tomek-szczesny/OpenUPS/hw/OpenUPS_bat/OpenUPS_bat.kicad_sch

## KiCad design hw/OpenUPS_bat/OpenUPS_bat.kicad_sch (2023-04-22, an earlier design)

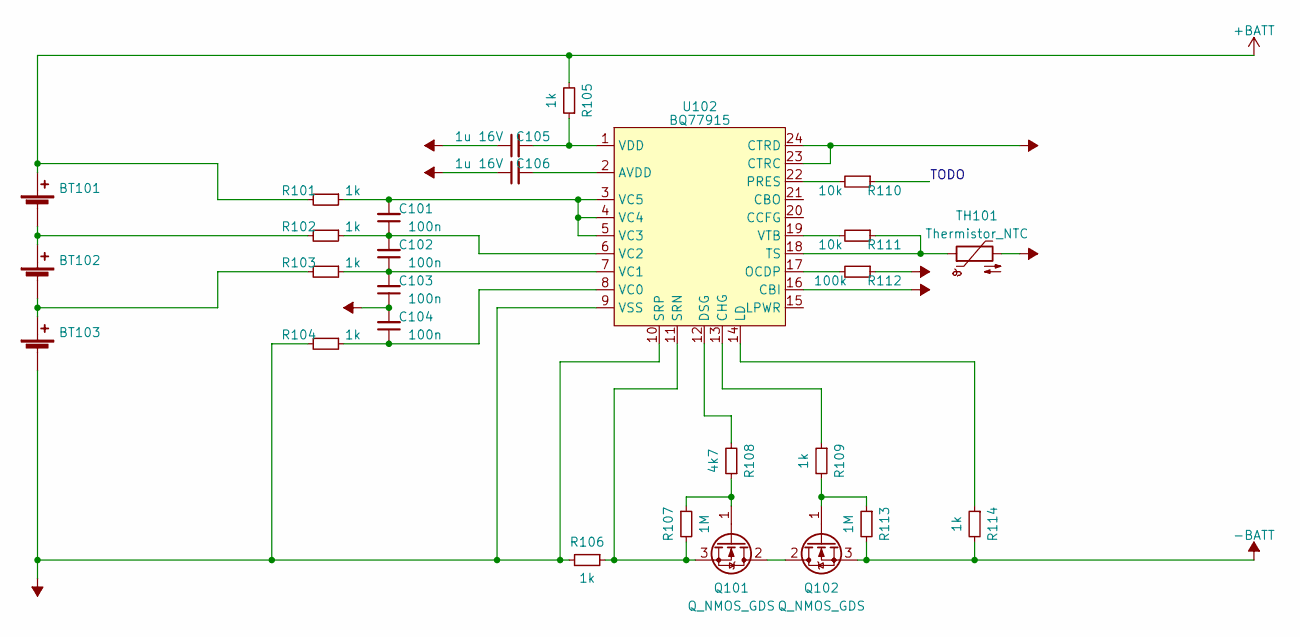
[picture p8: schematic OpenUPS_bat.kicad_sch]

Parts:
BT101, BT102, BT103: Battery_Cell
C101, C102, C103, C104: 100n; C_0603_1608Metric
C105, C106: 1u 16V; C_0603_1608Metric
Q101, Q102: Q_NMOS_GDS; TO-263-2
R101, R102, R103, R104, R105, R106, R109, R114: 1k; R_0603_1608Metric
R107, R113: 1M; R_0603_1608Metric
R108: 4k7; R_0603_1608Metric
R110, R111: 10k; R_0603_1608Metric
R112: 100k; R_0603_1608Metric
TH101: Thermistor_NTC
U102: BQ77915; TSSOP-24_4.4x7.8mm_P0.65mm

Connections:
+BATT: BT101.1 (+), R101.2, R105.2
-BATT: BT103.2 (-), C103.1, C104.2, C105.1, C106.1, Q102.3 (S), R104.2, R106.2, R112.1, R113.2, R114.2, TH101.2, U102.9 (VSS), U102.10 (SRP), U102.16 (CBI), U102.23 (CTRC), U102.24 (CTRD)
unnamed: BT101.2 (-), BT102.1 (+), R102.2
unnamed: BT102.2 (-), BT103.1 (+), R103.2
unnamed: C101.1, C102.2, R102.1, U102.6 (VC2)
unnamed: C101.2, R101.1, U102.3 (VC5), U102.4 (VC4), U102.5 (VC3)
unnamed: C102.1, C103.2, R103.1, U102.7 (VC1)
unnamed: C104.1, R104.1, U102.8 (VC0)
unnamed: C105.2, R105.1, U102.1 (VDD)
unnamed: C106.2, U102.2 (AVDD)
unnamed: Q101.1 (G), R107.1, R108.1
unnamed: Q101.2 (D), Q102.2 (D)
unnamed: Q101.3 (S), R106.1, R107.2, U102.11 (SRN)
unnamed: Q102.1 (G), R109.2, R113.1
unnamed: R108.2, U102.12 (DSG)
unnamed: R109.1, U102.13 (CHG)
unnamed: R110.2, U102.22 (PRES)
unnamed: R111.1, TH101.1, U102.18 (TS)
unnamed: R111.2, U102.19 (VTB)
unnamed: R112.2, U102.17 (OCDP)
unnamed: R114.1, U102.14 (LD)

Notes on the sheet:
TODO
