tomek-szczesny/OpenUPS/hw/OpenUPS_ups/5V_Buck.kicad_sch

## KiCad design hw/OpenUPS_ups/5V_Buck.kicad_sch (2023-05-13, an earlier design)

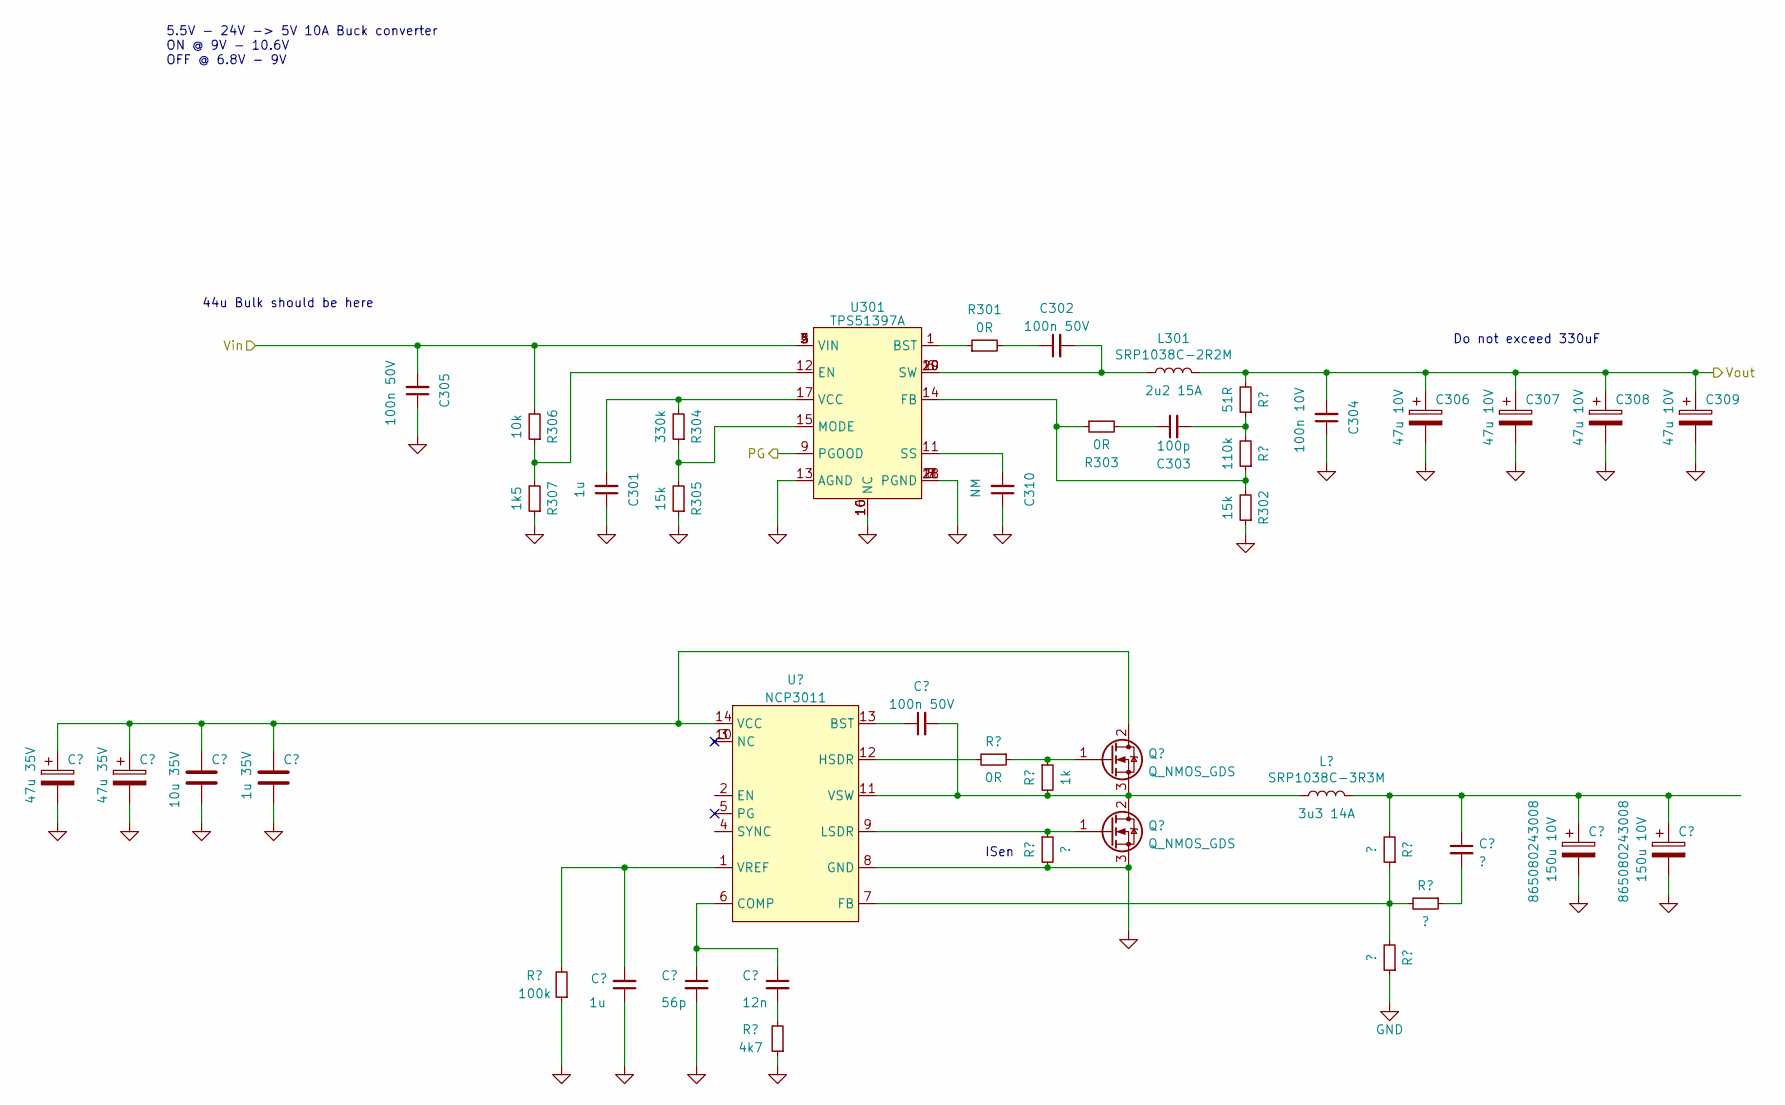
[picture p9: schematic 5V_Buck.kicad_sch]

Parts:
C301: 1u; C_0603_1608Metric
C302, C305: 100n 50V; C_0603_1608Metric
C303: 100p; C_0603_1608Metric
C304: 100n 10V; C_0603_1608Metric
C306, C307, C308, C309: CP_Elec_6.3x5.7
C310: NM; C_0603_1608Metric
L301: SRP1038C-2R2M; L_Bourns_SRP1038C_10.0x10.0mm
R301, R303: 0R; R_0603_1608Metric
R302, R305: 15k; R_0603_1608Metric
R304: 330k; R_0603_1608Metric
R306: 10k; R_0603_1608Metric
R307: 1k5; R_0603_1608Metric
U301: TPS51397A; Texas-VQFN-HR-20_EP_3x3_Pitch0.45mm

Connections:
GND: C301.1, C304.1, C305.1, C306.2, C307.2, C308.2, C309.2, C310.1, R302.1, R305.1, R307.1, U301.7 (PGND), U301.8 (PGND), U301.10 (NC), U301.13 (AGND), U301.16 (NC), U301.18 (PGND), U301.21 (PGND)
unnamed: C301.2, R304.2, U301.17 (VCC)
unnamed: C302.1, R301.2
unnamed: C302.2, L301.1, U301.6 (SW), U301.19 (SW), U301.20 (SW)
unnamed: C303.1, R303.2
unnamed: C310.2, U301.11 (SS)
unnamed: R301.1, U301.1 (BST)
unnamed: R302.2, R303.1, U301.14 (FB)
unnamed: R304.1, R305.2, U301.15 (MODE)
unnamed: R306.1, R307.2, U301.12 (EN)
PG: U301.9 (PGOOD)
Vin: C305.2, R306.2, U301.2 (VIN), U301.3 (VIN), U301.4 (VIN), U301.5 (VIN)
Vout: C304.2, C306.1, C307.1, C308.1, C309.1, L301.2

Notes on the sheet:
5.5V - 24V -> 5V 10A Buck converter ON @ 9V - 10.6V OFF @ 6.8V - 9V
Do not exceed 330uF
ISen
44u Bulk should be here
