tomek-szczesny/OpenUPS/hw/OpenUPS_ups/12V_Buck.kicad_sch

## KiCad design hw/OpenUPS_ups/12V_Buck.kicad_sch (2023-04-21, an earlier design)

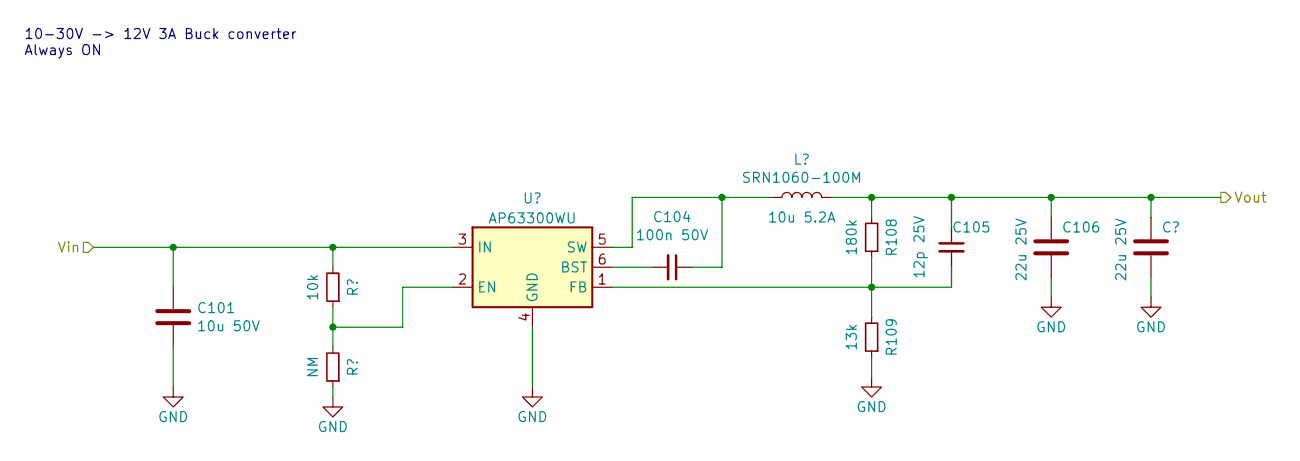
[picture p10: schematic 12V_Buck.kicad_sch]

Parts:
C101: 10u 50V; C_1206_3216Metric
C104: 100n 50V; C_0603_1608Metric
C105: 12p 25V; C_0603_1608Metric
C106: 22u 25V; C_1206_3216Metric
R108: 180k; R_0603_1608Metric
R109: 13k; R_0603_1608Metric

Connections:
GND: C101.2, C106.2, R109.1
unnamed: C105.2, R108.1, R109.2
Vin: C101.1
Vout: C105.1, C106.1, R108.2

Notes on the sheet:
10-30V -> 12V 3A Buck converter Always ON
