tomek-szczesny/OpenUPS/hw/OpenUPS_ups/12V_Buck_Boost.kicad_sch

## KiCad design hw/OpenUPS_ups/12V_Buck_Boost.kicad_sch (2023-05-13, an earlier design)

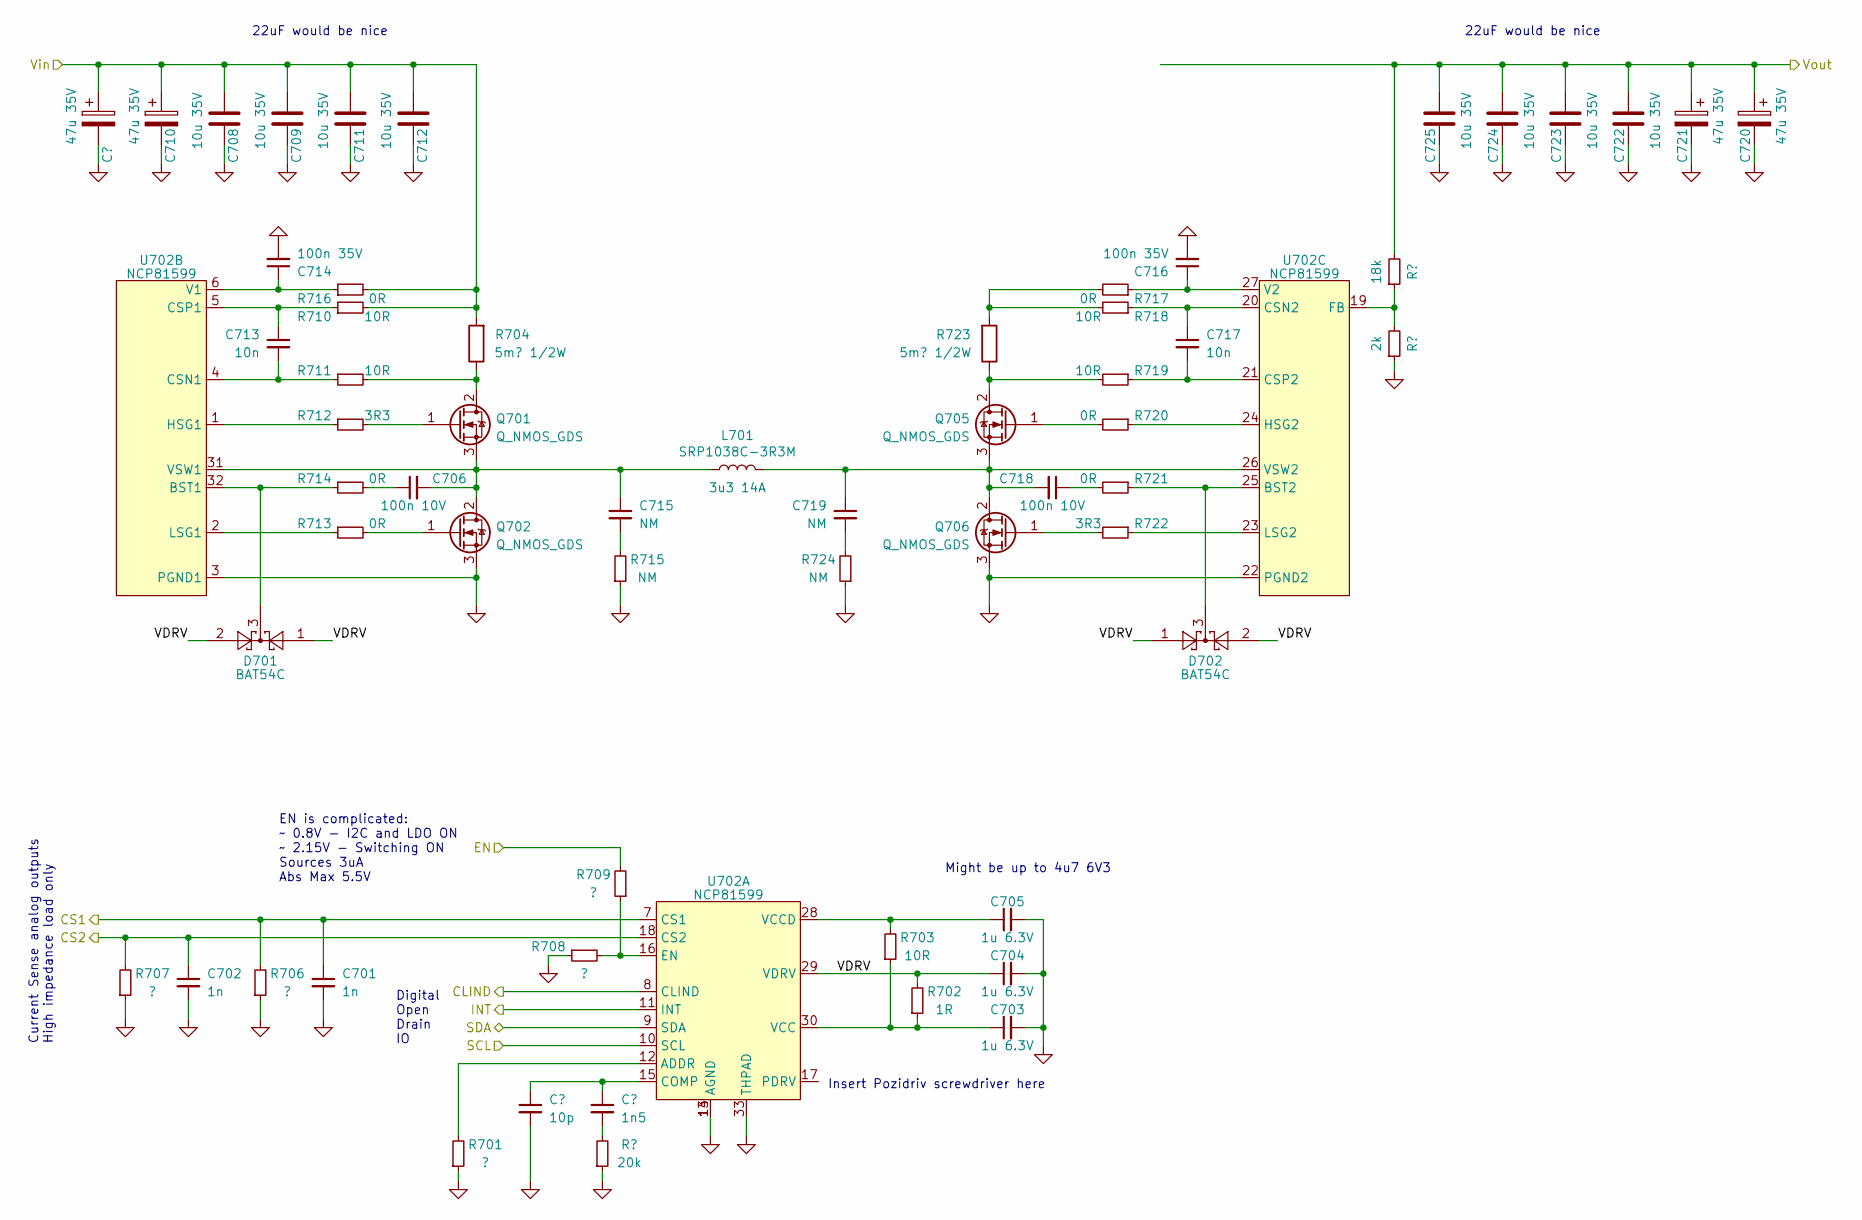
[picture p11: schematic 12V_Buck_Boost.kicad_sch]

Parts:
C701, C702: 1n; C_0603_1608Metric
C703, C704, C705: 1u 6.3V; C_0603_1608Metric
C706, C718: 100n 10V; C_0603_1608Metric
C708, C709, C711, C712, C722, C723, C724, C725: 10u 35V; C_1206_3216Metric
C710, C720, C721: 47u 35V; CP_Elec_6.3x7.7
C713, C717: 10n; C_0603_1608Metric
C714, C716: 100n 35V; C_0603_1608Metric
C715, C719: NM; C_0603_1608Metric
D701, D702: BAT54C; SOT-23
L701: SRP1038C-3R3M; L_Bourns_SRP1038C_10.0x10.0mm
Q701, Q702, Q705, Q706: Q_NMOS_GDS; TO-263-2
R701, R706, R707, R708, R709: ?; R_0603_1608Metric
R702: 1R; R_0603_1608Metric
R703, R710, R711, R718, R719: 10R; R_0603_1608Metric
R704, R723: 5m? 1/2W; R_2512_6332Metric
R712, R722: 3R3; R_0603_1608Metric
R713, R714, R716, R717, R720, R721: 0R; R_0603_1608Metric
R715, R724: NM; R_0603_1608Metric
U702: NCP81599; QFN-32-1EP_5x5mm_P0.5mm_EP3.7x3.7mm

Connections:
CLIND: U702.8 (CLIND)
CS1: C701.1, R706.2, U702.7 (CS1)
CS2: C702.1, R707.2, U702.18 (CS2)
EN: R709.2
GND: C701.2, C702.2, C703.2, C704.2, C705.2, C710.2, C711.2, C712.2, C714.2, C716.2, C720.2, C721.2, C722.2, C723.2, C724.2, C725.2, Q702.3 (S), Q706.3 (S), R701.1, R706.1, R707.1, R708.1, R715.1, R724.1, U702.3 (PGND1), U702.13 (AGND), U702.14 (AGND), U702.22 (PGND2), U702.33 (THPAD)
INT: U702.11 (INT)
unnamed: C703.1, R702.1, R703.1, U702.30 (VCC)
unnamed: C705.1, R703.2, U702.28 (VCCD)
unnamed: C706.1, R714.2
unnamed: C706.2, C715.1, L701.1, Q701.3 (S), Q702.2 (D), U702.31 (VSW1)
unnamed: C713.1, R710.1, U702.5 (CSP1)
unnamed: C713.2, R711.1, U702.4 (CSN1)
unnamed: C714.1, R716.1, U702.6 (V1)
unnamed: C715.2, R715.2
unnamed: C716.1, R717.1, U702.27 (V2)
unnamed: C717.1, R718.1, U702.20 (CSN2)
unnamed: C717.2, R719.1, U702.21 (CSP2)
unnamed: C718.1, R721.2
unnamed: C718.2, C719.1, L701.2, Q705.3 (S), Q706.2 (D), U702.26 (VSW2)
unnamed: C719.2, R724.2
unnamed: D701.3, R714.1, U702.32 (BST1)
unnamed: D702.3, R721.1, U702.25 (BST2)
unnamed: Q701.1 (G), R712.2
unnamed: Q701.2 (D), R704.1, R711.2
unnamed: Q702.1 (G), R713.2
unnamed: Q705.1 (G), R720.2
unnamed: Q705.2 (D), R719.2, R723.1
unnamed: Q706.1 (G), R722.2
unnamed: R701.2, U702.12 (ADDR)
unnamed: R708.2, R709.1, U702.16 (EN)
unnamed: R712.1, U702.1 (HSG1)
unnamed: R713.1, U702.2 (LSG1)
unnamed: R717.2, R718.2, R723.2
unnamed: R720.1, U702.24 (HSG2)
unnamed: R722.1, U702.23 (LSG2)
SCL: U702.10 (SCL)
SDA: U702.9 (SDA)
VDRV: C704.1, D701.1, D701.2, D702.1, D702.2, R702.2, U702.29 (VDRV)
Vin: C708.1, C709.1, C710.1, C711.1, C712.1, R704.2, R710.2, R716.2
Vout: C720.1, C721.1, C722.1, C723.1, C724.1, C725.1

Notes on the sheet:
Insert Pozidriv screwdriver here
Digital Open Drain IO
Might be up to 4u7 6V3
Current Sense analog outputs High impedance load only
22uF would be nice
EN is complicated: ~ 0.8V - I2C and LDO ON ~ 2.15V - Switching ON Sources 3uA Abs Max 5.5V
