tomek-szczesny/OpenUPS/hw/OpenUPS_ups/Bat_Charger.kicad_sch

## KiCad design hw/OpenUPS_ups/Bat_Charger.kicad_sch (2023-05-13, an earlier design)

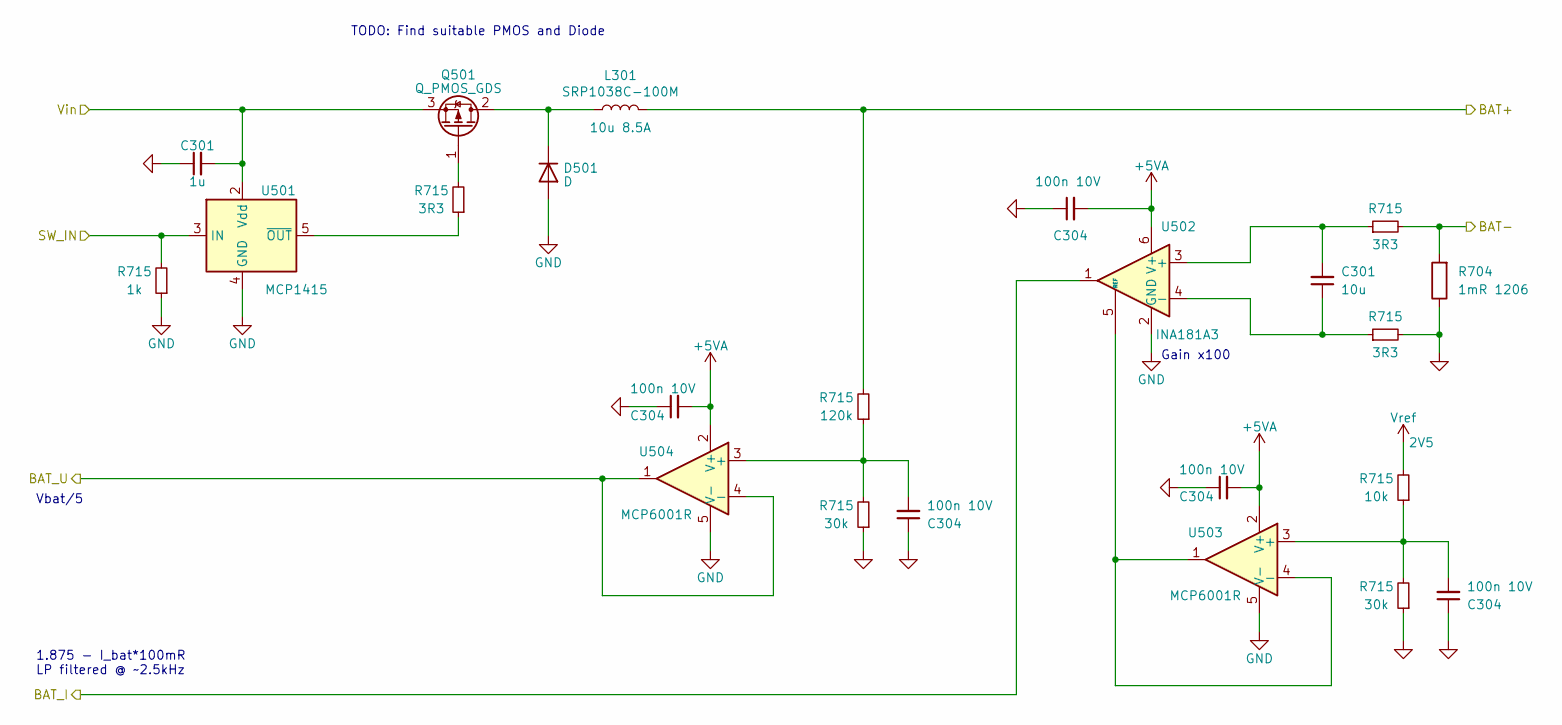
[picture p12: schematic Bat_Charger.kicad_sch]

Parts:
C301: 1u; C_0603_1608Metric
C304: 100n 10V; C_0603_1608Metric
D501: D
L301: SRP1038C-100M; L_Bourns_SRP1038C_10.0x10.0mm
Q501: Q_PMOS_GDS
R704: 1mR 1206; R_1206_3216Metric
R715: 3R3; R_0603_1608Metric
U501: MCP1415; SOT-23-5
U502: INA181A3; SOT-23-6
U503, U504: MCP6001R; SOT-23-5

Connections:
+5VA: C304.2, U502.6 (V+), U503.2 (V+), U504.2 (V+)
BAT+: L301.2, R715.2
BAT-: R704.2, R715.2
BAT_I: U502.1
BAT_U: U504.1, U504.4 (-)
GND: C301.1, C304.1, D501.2 (A), R704.1, R715.1, R715.2, U501.4 (GND), U502.2 (GND), U503.5 (V-), U504.5 (V-)
unnamed: C301.1, R715.1, U502.4 (-)
unnamed: C301.2, R715.1, U502.3 (+)
unnamed: C304.2, R715.1, R715.2, U503.3 (+), U504.3 (+)
unnamed: D501.1 (K), L301.1, Q501.2 (D)
unnamed: Q501.1 (G), R715.2
unnamed: R715.1, U501.5 (~OUT)
unnamed: U502.5 (REF), U503.1, U503.4 (-)
SW_IN: R715.2, U501.3 (IN)
Vin: C301.2, Q501.3 (S), U501.2 (Vdd)
Vref: R715.2

Notes on the sheet:
1.875 - I_bat*100mR LP filtered @ ~2.5kHz
Vbat/5
TODO: Find suitable PMOS and Diode
Gain x100
