tomek-szczesny/OpenUPS/hw/OpenUPS_ups/aux.kicad_sch

## KiCad design hw/OpenUPS_ups/aux.kicad_sch (2023-05-13)

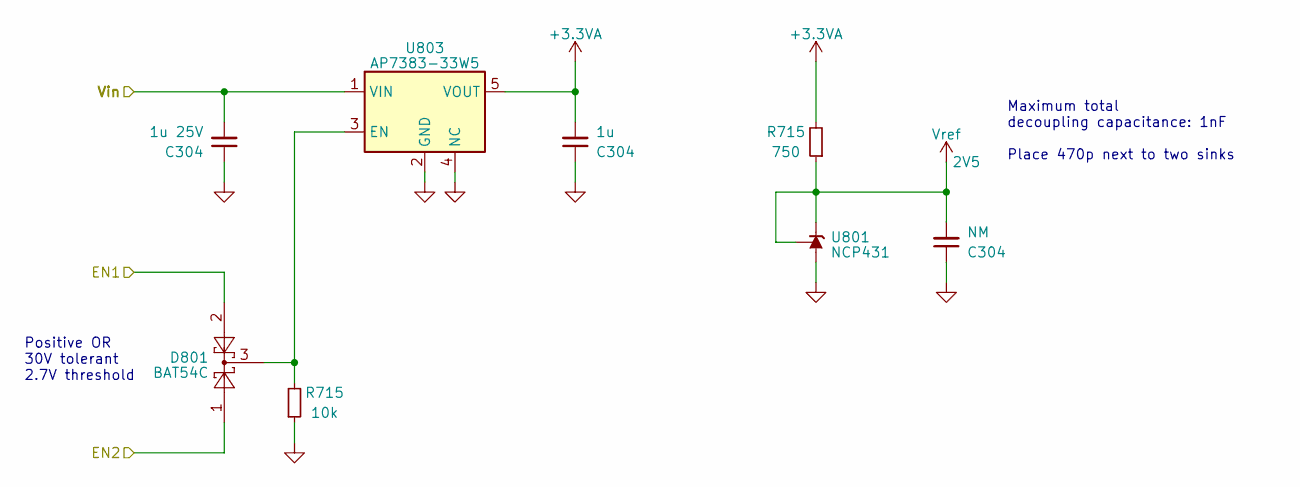
[picture p13: schematic aux.kicad_sch]

Parts:
C304: 1u; C_0603_1608Metric
D801: BAT54C; SOT-23
R715: 10k; R_0603_1608Metric
U801: NCP431; SOT-23
U803: AP7383-33W5; SOT-23-5

Connections:
+3.3VA: C304.2, R715.2, U803.5 (VOUT)
EN1: D801.2
EN2: D801.1
GND: C304.1, R715.1, U801.3 (A), U803.2 (GND), U803.4 (NC)
unnamed: D801.3, R715.2, U803.3 (EN)
Vin: C304.2, U803.1 (VIN)
Vref: C304.2, R715.1, U801.1 (REF), U801.2 (K)

Notes on the sheet:
Maximum total decoupling capacitance: 1nF Place 470p next to two sinks
Positive OR 30V tolerant 2.7V threshold
