tomek-szczesny/OpenUPS/hw/OpenUPS_ups/ext_i2c.kicad_sch

## KiCad design hw/OpenUPS_ups/ext_i2c.kicad_sch (2023-05-13)

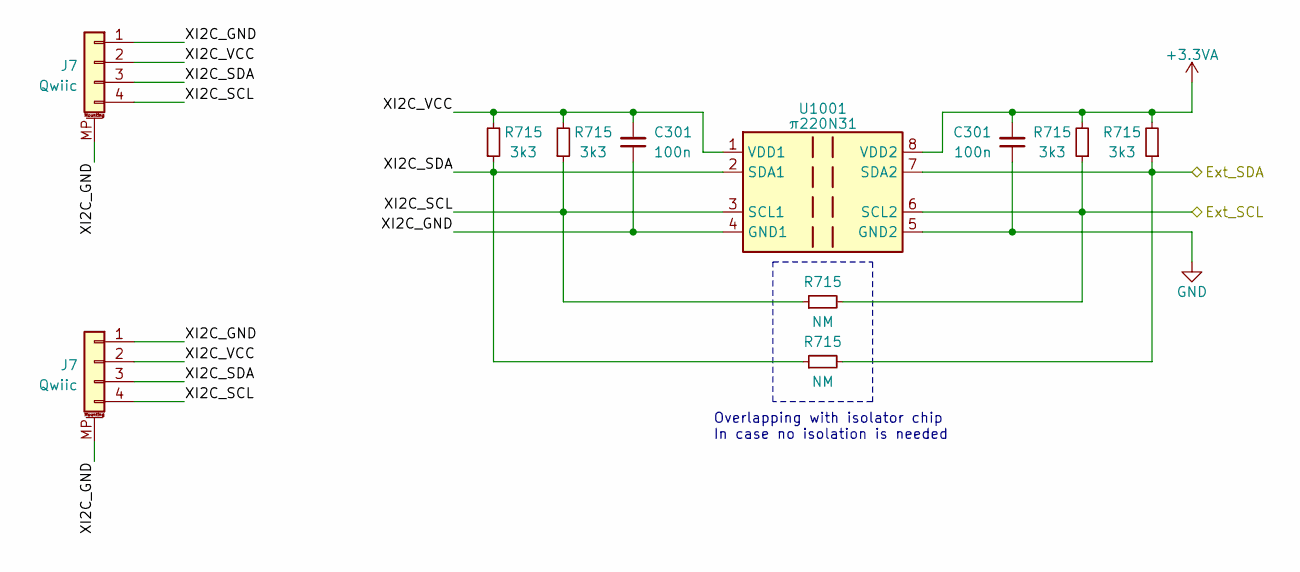
[picture p14: schematic ext_i2c.kicad_sch]

Parts:
C301: 100n; C_0603_1608Metric
J7: Qwiic; JST_SH_SM04B-SRSS-TB_1x04-1MP_P1.00mm_Horizontal
R715: NM
U1001: π220N31; SO-8_3.9x4.9mm_P1.27mm

Connections:
+3.3VA: C301.2, R715.2, U1001.8 (VDD2)
Ext_SCL: R715.1, R715.2, U1001.6 (SCL2)
Ext_SDA: R715.1, R715.2, U1001.7 (SDA2)
GND: C301.1, U1001.5 (GND2)
XI2C_GND: C301.1, J7.1, J7.MP (MountPin), U1001.4 (GND1)
XI2C_SCL: J7.4, R715.1, U1001.3 (SCL1)
XI2C_SDA: J7.3, R715.1, U1001.2 (SDA1)
XI2C_VCC: C301.2, J7.2, R715.2, U1001.1 (VDD1)

Notes on the sheet:
Overlapping with isolator chip In case no isolation is needed
