tomek-szczesny/OpenUPS/hw/OpenUPS_ups/fans.kicad_sch

## KiCad design hw/OpenUPS_ups/fans.kicad_sch (2023-05-13)

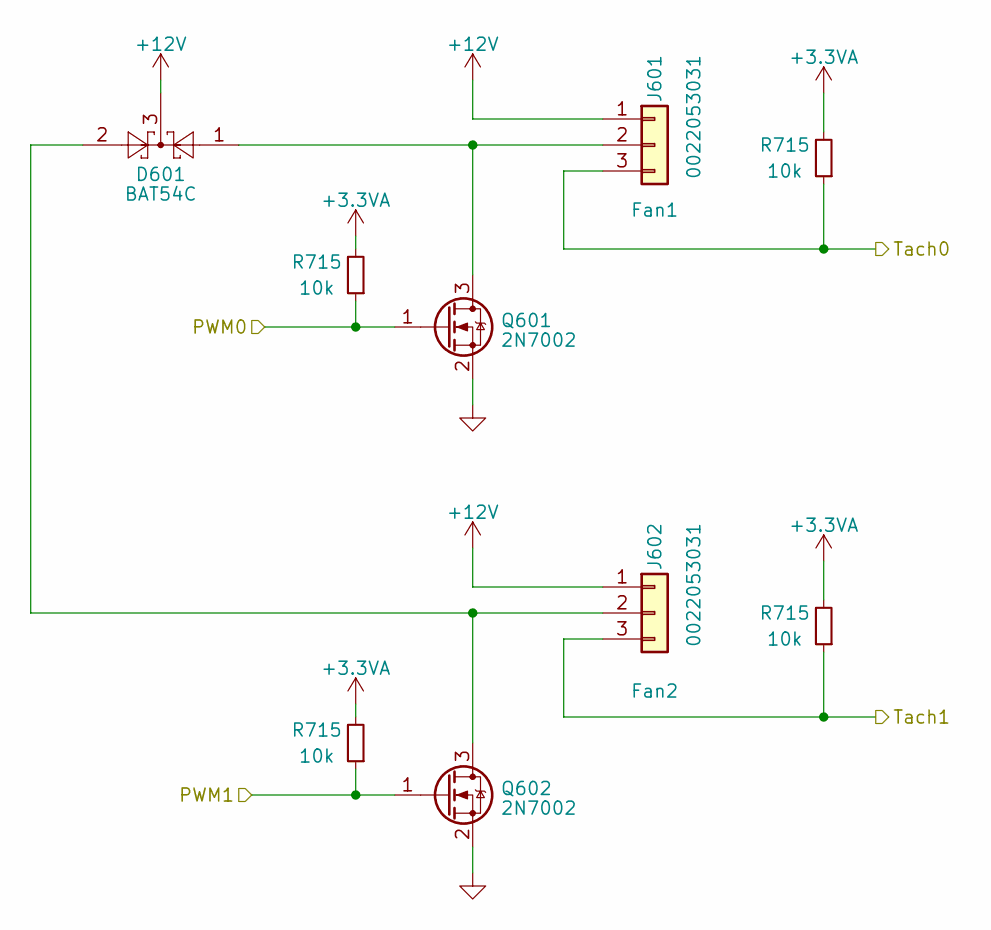
[picture p15: schematic fans.kicad_sch]

Parts:
D601: BAT54C; SOT-23
J601, J602: 0022053031; Molex-22-05-3031-MFG
Q601, Q602: 2N7002; SOT-23
R715: 10k; R_0603_1608Metric

Connections:
+3.3VA: R715.2
+12V: D601.3, J601.1, J602.1
GND: Q601.2 (S), Q602.2 (S)
unnamed: D601.1, J601.2, Q601.3 (D)
unnamed: D601.2, J602.2, Q602.3 (D)
PWM0: Q601.1 (G), R715.1
PWM1: Q602.1 (G), R715.1
Tach0: J601.3, R715.1
Tach1: J602.3, R715.1
