tomek-szczesny/OpenUPS/hw/OpenUPS_ups/leds.kicad_sch

## KiCad design hw/OpenUPS_ups/leds.kicad_sch (2023-05-13)

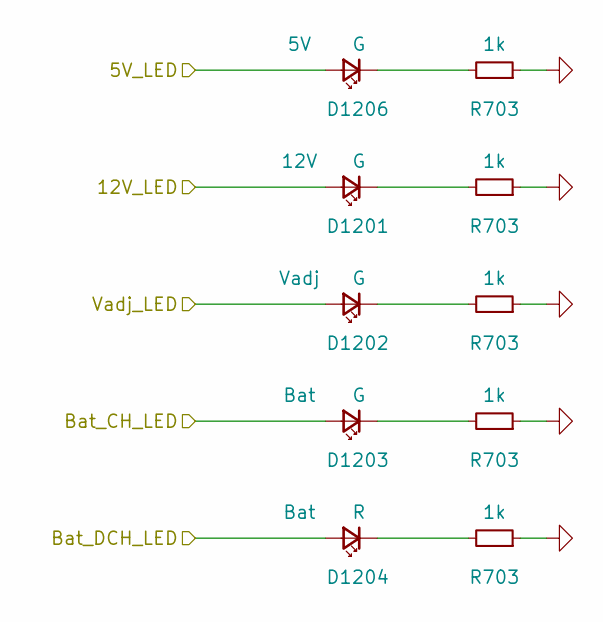
[picture p16: schematic leds.kicad_sch]

Parts:
D1201, D1202, D1203, D1206: G; LED_0603_1608Metric
D1204: R; LED_0603_1608Metric
R703: 1k; R_0603_1608Metric

Connections:
5V_LED: D1206.2 (A)
12V_LED: D1201.2 (A)
Bat_CH_LED: D1203.2 (A)
Bat_DCH_LED: D1204.2 (A)
GND: R703.1
unnamed: D1201.1 (K), R703.2
unnamed: D1202.1 (K), R703.2
unnamed: D1203.1 (K), R703.2
unnamed: D1204.1 (K), R703.2
unnamed: D1206.1 (K), R703.2
Vadj_LED: D1202.2 (A)
