tomek-szczesny/OpenUPS/hw/OpenUPS_ups/oring.kicad_sch

## KiCad design hw/OpenUPS_ups/oring.kicad_sch (2023-05-13)

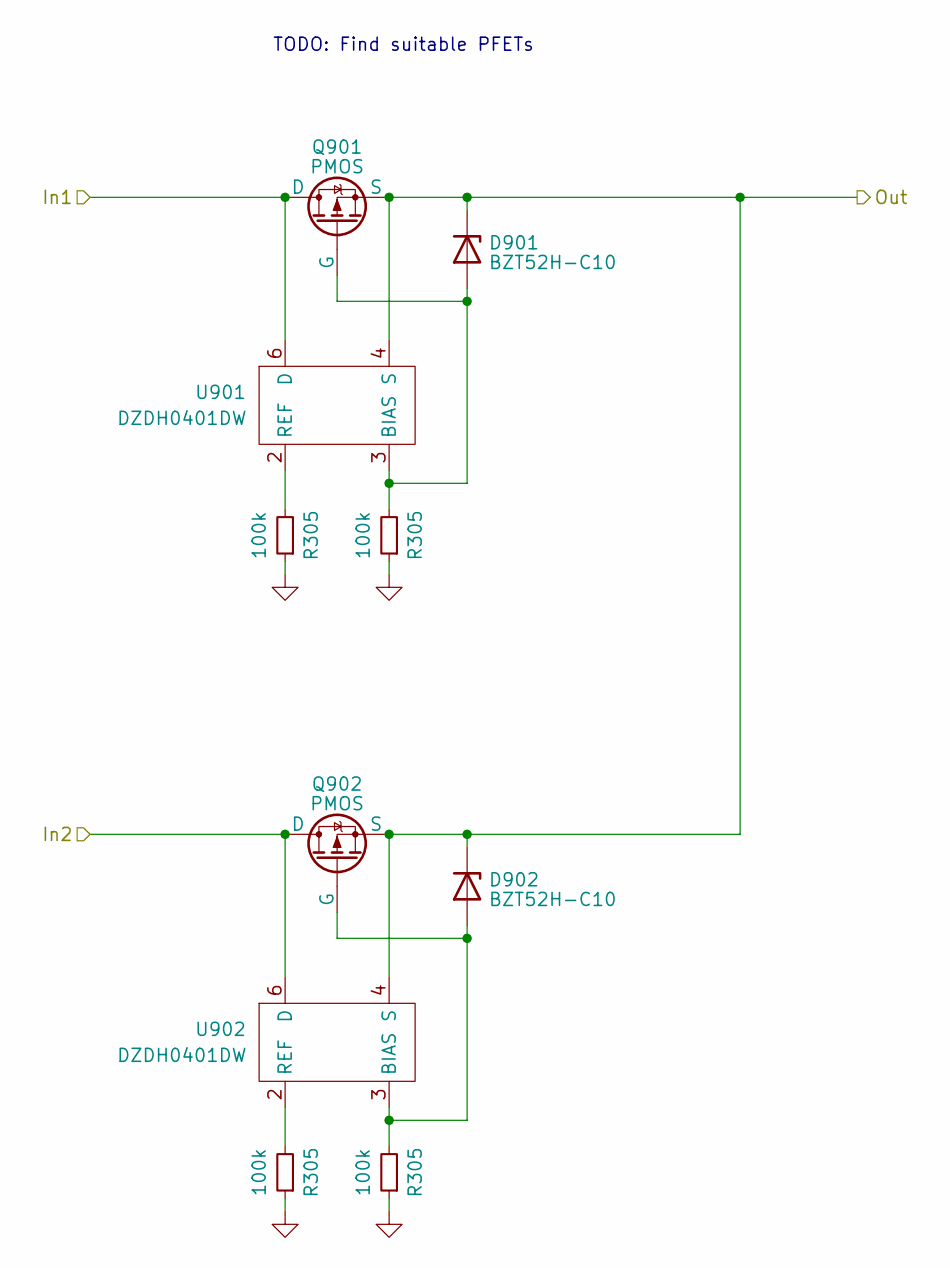
[picture p17: schematic oring.kicad_sch]

Parts:
D901, D902: BZT52H-C10; D_SOD-123F
Q901, Q902: PMOS
R305: 100k; R_0603_1608Metric
U901, U902: DZDH0401DW; SOT-363_SC-70-6

Connections:
GND: R305.1
In1: Q901.1 (D), U901.6 (D)
In2: Q902.1 (D), U902.6 (D)
unnamed: D901.2 (A), Q901.2 (G), R305.2, U901.3 (BIAS)
unnamed: D902.2 (A), Q902.2 (G), R305.2, U902.3 (BIAS)
unnamed: R305.2, U901.2 (REF), U902.2 (REF)
Out: D901.1 (K), D902.1 (K), Q901.3 (S), Q902.3 (S), U901.4 (S), U902.4 (S)

Notes on the sheet:
TODO: Find suitable PFETs
