tomek-szczesny/OpenUPS/hw/OpenUPS_ups/prog.kicad_sch

## KiCad design hw/OpenUPS_ups/prog.kicad_sch (2023-05-13)

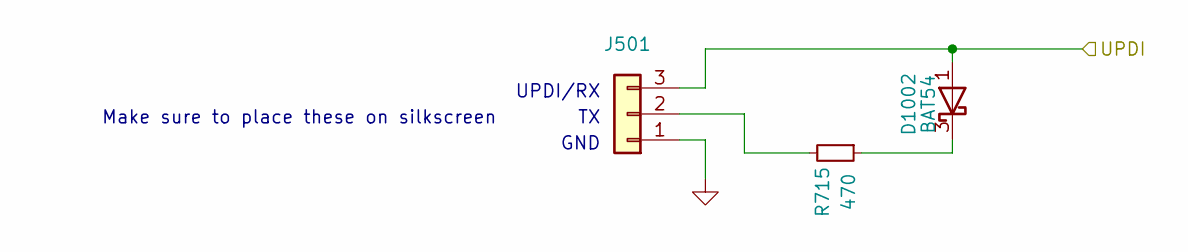
[picture p18: schematic prog.kicad_sch]

Parts:
D1002: BAT54; SOT-23
J501: Conn_01x03; PinHeader_1x03_P2.54mm_Vertical
R715: 470; R_0603_1608Metric

Connections:
GND: J501.1
unnamed: D1002.3 (K), R715.1
unnamed: J501.2, R715.2
UPDI: D1002.1 (A), J501.3

Notes on the sheet:
UPDI/RX
Make sure to place these on silkscreen
GND
