tomek-szczesny/OpenUPS/hw/OpenUPS_ups/usbc.kicad_sch

## KiCad design hw/OpenUPS_ups/usbc.kicad_sch (2023-05-13)

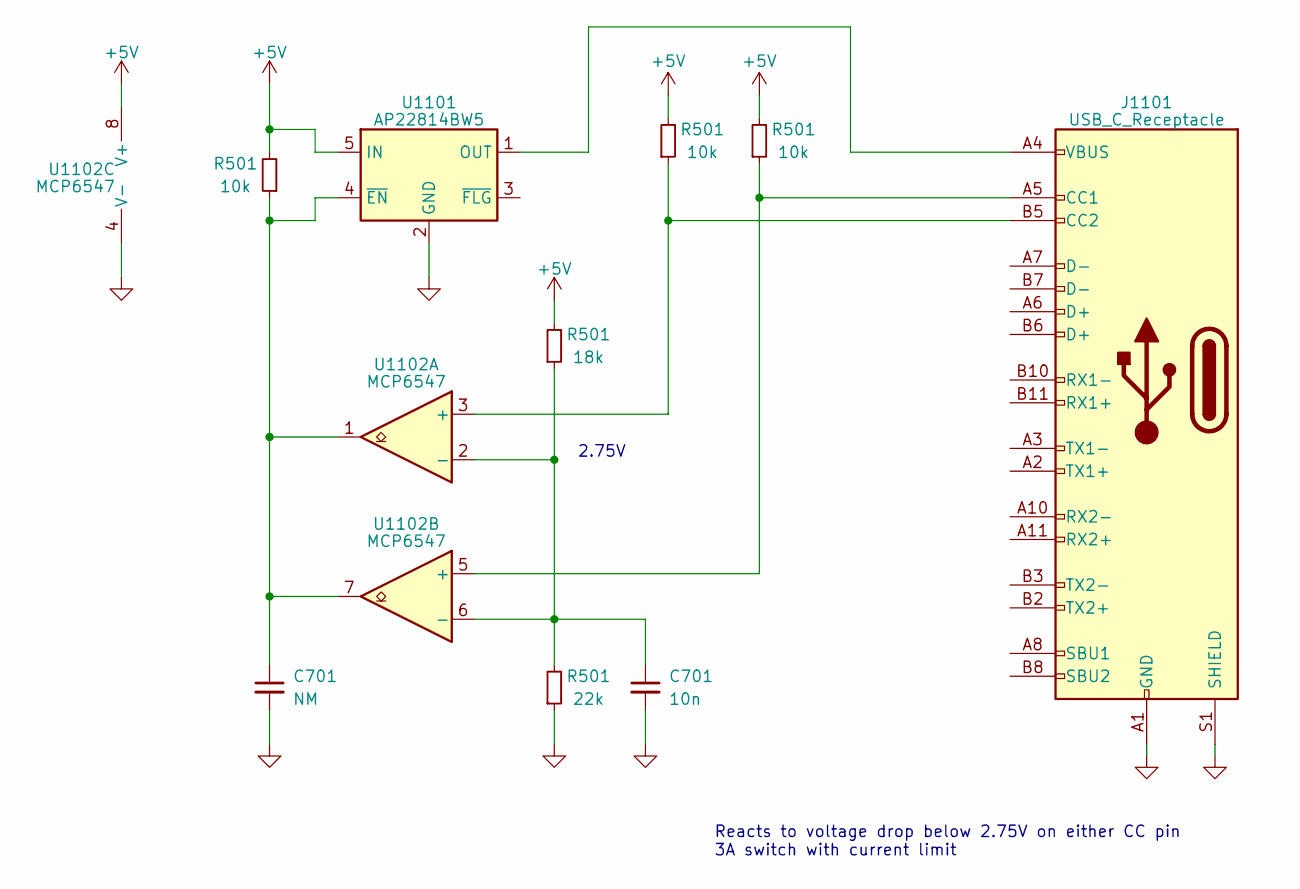
[picture p19: schematic usbc.kicad_sch]

Parts:
C701: 10n; C_0603_1608Metric
J1101: USB_C_Receptacle
R501: 18k; R_0603_1608Metric
U1101: AP22814BW5; SOT-23-5
U1102: MCP6547; SO-8_3.9x4.9mm_P1.27mm

Connections:
+5V: R501.2, U1101.5 (IN), U1102.8 (V+)
GND: C701.2, J1101.A1 (GND), J1101.A12 (GND), J1101.B1 (GND), J1101.B12 (GND), J1101.S1 (SHIELD), R501.1, U1101.2 (GND), U1102.4 (V-)
unnamed: C701.1, R501.1, R501.2, U1101.4 (~EN), U1102.1, U1102.2 (-), U1102.6 (-), U1102.7
unnamed: J1101.A4 (VBUS), J1101.A9 (VBUS), J1101.B4 (VBUS), J1101.B9 (VBUS), U1101.1 (OUT)
unnamed: J1101.A5 (CC1), R501.1, U1102.5 (+)
unnamed: J1101.B5 (CC2), R501.1, U1102.3 (+)

Notes on the sheet:
2.75V
Reacts to voltage drop below 2.75V on either CC pin 3A switch with current limit
