tomek-szczesny/OpenUPS/fw/LM75BTP.h

/*
 * Copyright (c) 2023 by the OpenUPS Developers All rights reserved.
 *
 *        File:  LM75B.h
 * Description:  NXP LM75B Register Map per Datasheet
 *
*/

#define LM75B_ADDR      0x48

#define LM75B_TEMP      0x00
#define LM75B_CONFIG    0x01
#define LM75B_THYST     0x02
#define LM75B_TOS       0x03
